APivetta/robot-arm/modelos/stl/lower_pin.stl

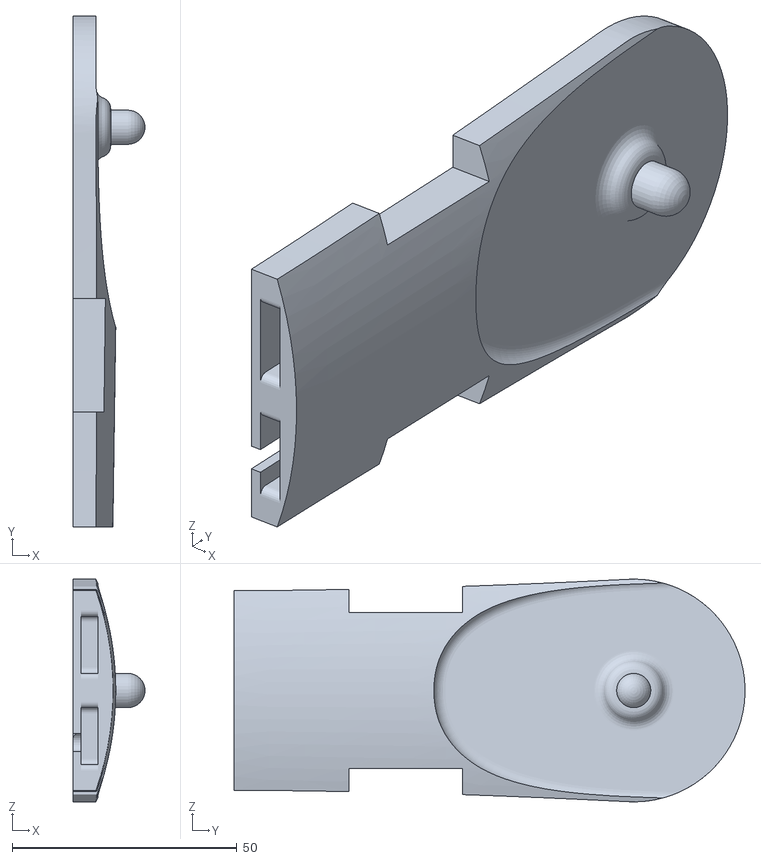
[picture p16: CAD file, 2019-10-16]
modelos/stl/lower_pin.stl
16.0 x 113.6 x 49.5
