APivetta/robot-arm/modelos/stl/base_bottom_rotate.stl

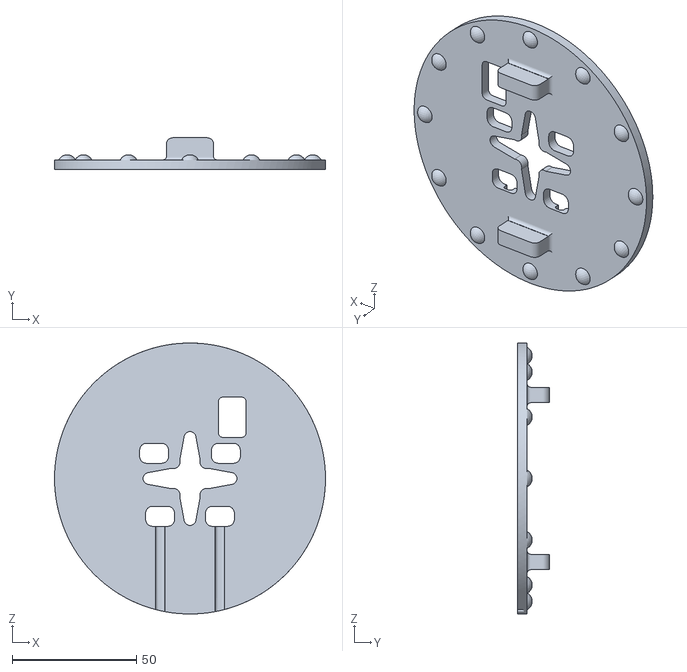
[picture p17: CAD file, 2019-10-16]
modelos/stl/base_bottom_rotate.stl
109.2 x 12.7 x 109.2
