APivetta/robot-arm/modelos/stl/base_bottom_rotate_box.stl

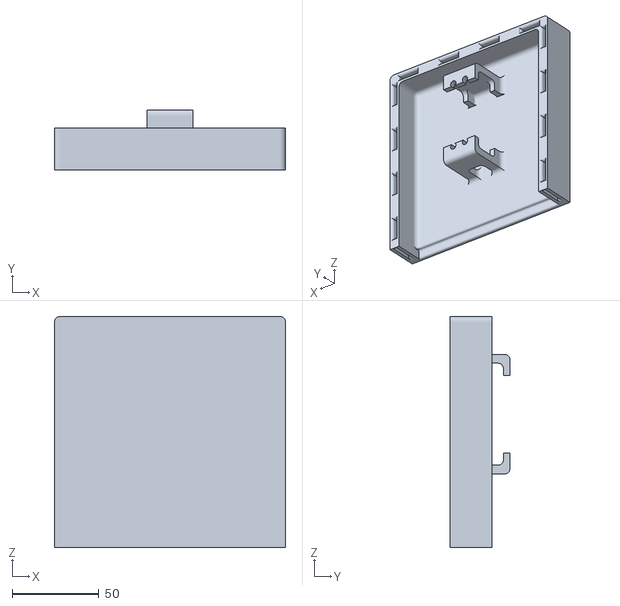
[picture p18: CAD file, 2019-10-16]
modelos/stl/base_bottom_rotate_box.stl
133.4 x 34.6 x 133.4
