APivetta/robot-arm/modelos/stl/mid_up_horn.stl

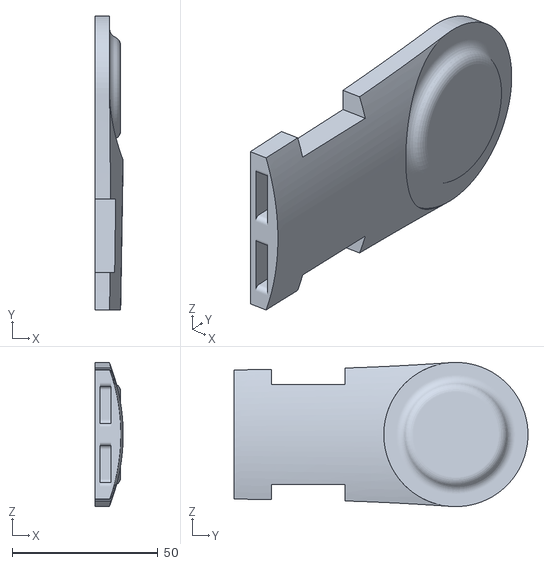
[picture p19: CAD file, 2019-10-16]
modelos/stl/mid_up_horn.stl
9.75 x 101.0 x 49.5
