APivetta/robot-arm/modelos/stl/upper_servo.stl

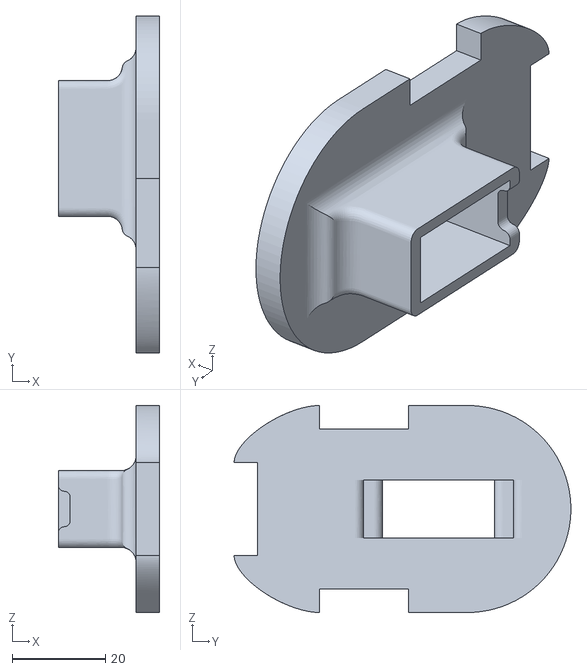
[picture p20: CAD file, 2019-10-16]
modelos/stl/upper_servo.stl
21.8 x 72.3 x 44.5
