APivetta/robot-arm/modelos/stl/upper_front.stl

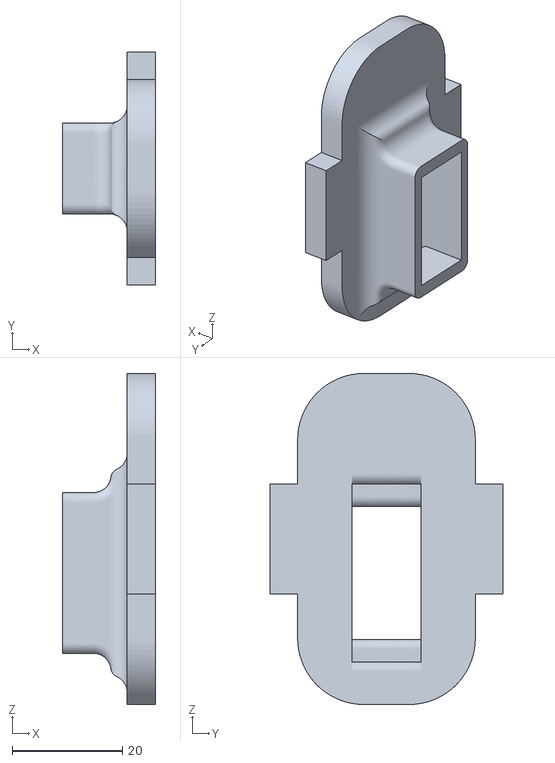
[picture p21: CAD file, 2019-10-16]
modelos/stl/upper_front.stl
16.8 x 42.2 x 60.0
