APivetta/robot-arm/modelos/stl/base_top_rotate.stl

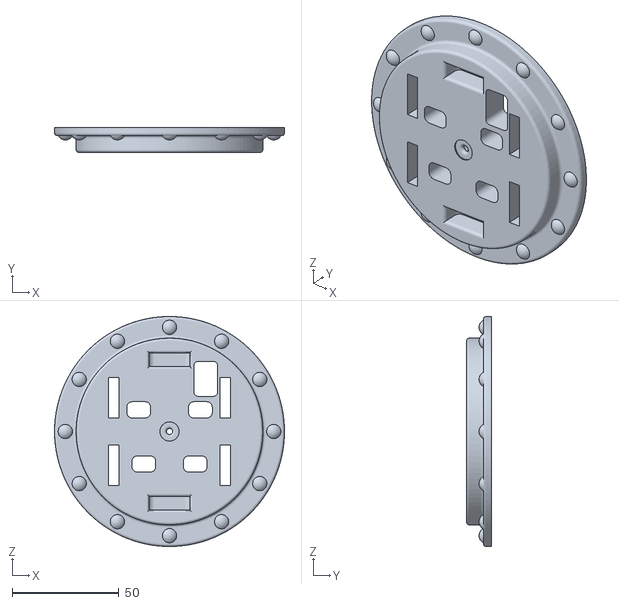
[picture p22: CAD file, 2019-10-16]
modelos/stl/base_top_rotate.stl
107.9 x 11.7 x 107.9
