APivetta/robot-arm/modelos/stl/upper_pin.stl

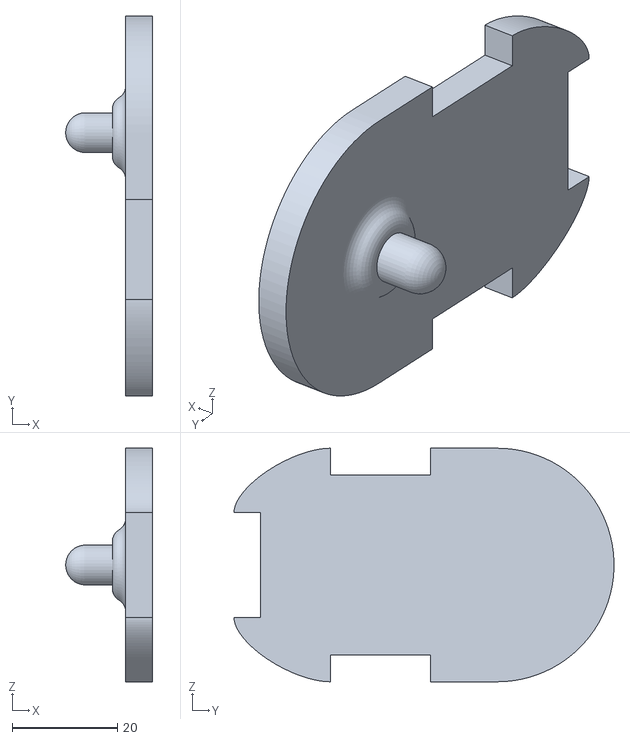
[picture p23: CAD file, 2019-10-16]
modelos/stl/upper_pin.stl
16.5 x 72.3 x 44.5
