APivetta/robot-arm/modelos/stl/base_servo_mount_mirror.stl

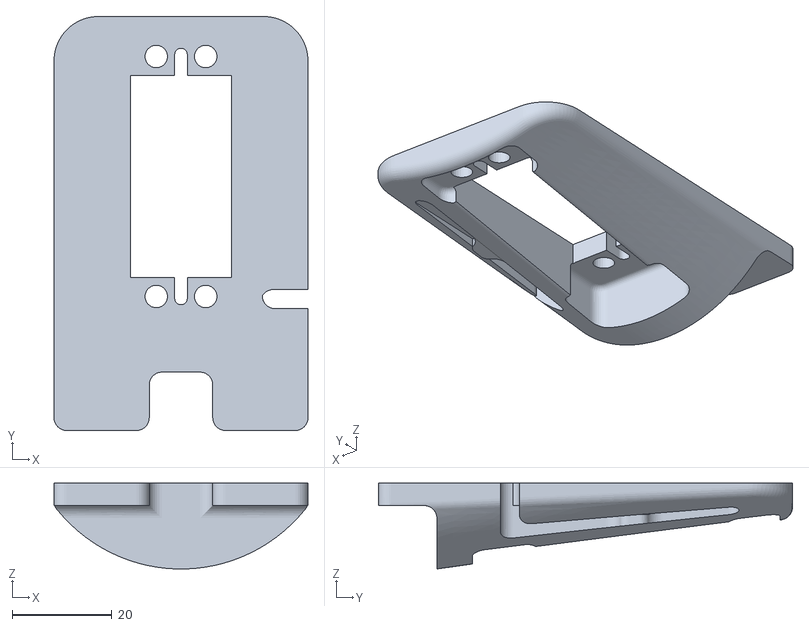
[picture p24: CAD file, 2019-10-16]
modelos/stl/base_servo_mount_mirror.stl
50.8 x 82.8 x 17.2
