APivetta/robot-arm/modelos/stl/base_top_rotate_box.stl

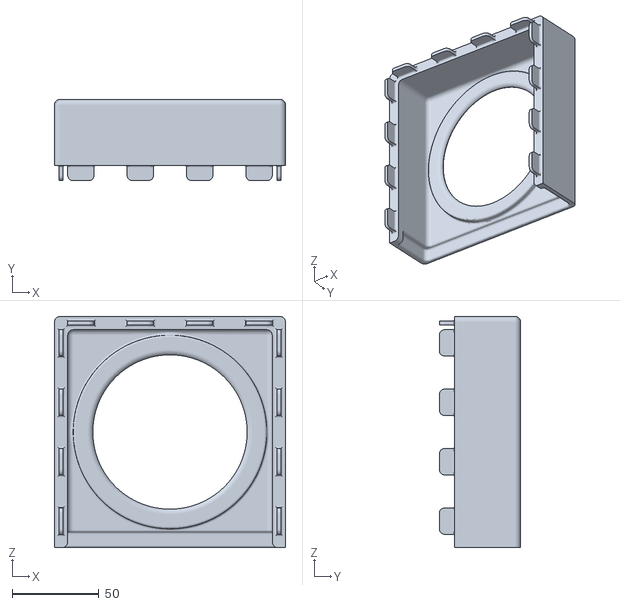
[picture p25: CAD file, 2019-10-16]
modelos/stl/base_top_rotate_box.stl
133.4 x 47.0 x 133.4
