APivetta/robot-arm/modelos/stl/mid_up_brace.stl

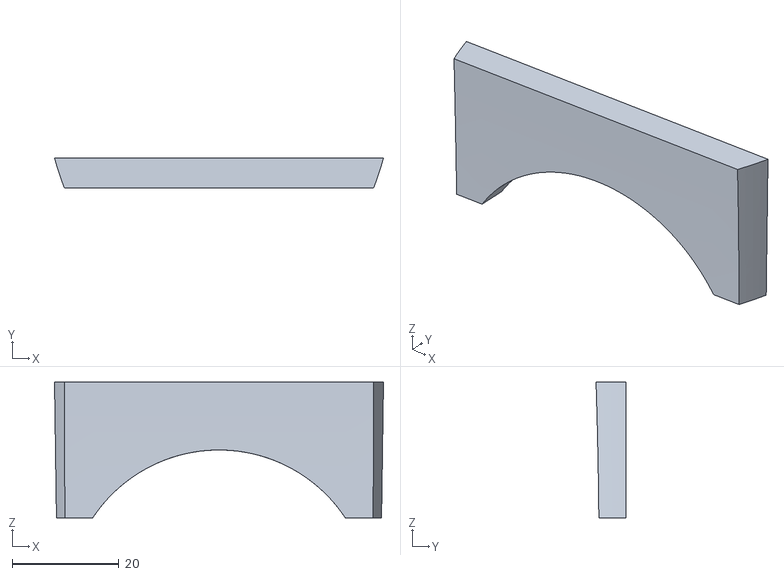
[picture p26: CAD file, 2019-10-16]
modelos/stl/mid_up_brace.stl
61.6 x 5.61 x 25.4
