APivetta/robot-arm/modelos/stl/mid_low_horn.stl

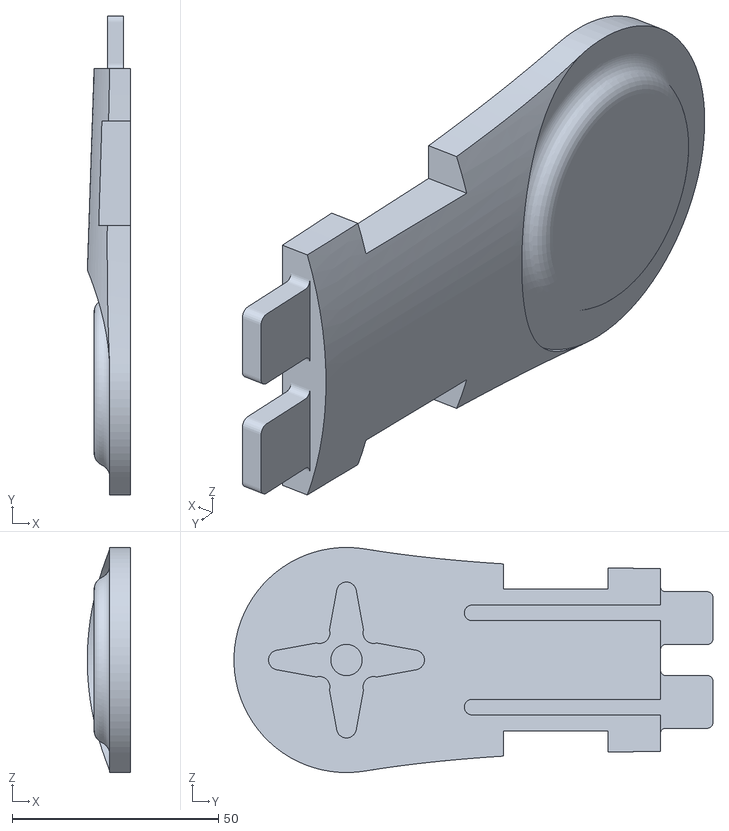
[picture p27: CAD file, 2019-10-16]
modelos/stl/mid_low_horn.stl
10.5 x 116.2 x 54.6
